cclaunch/PC1053/mosfet_board.kicad_sch

## KiCad design mosfet_board.kicad_sch (2026-06-03)

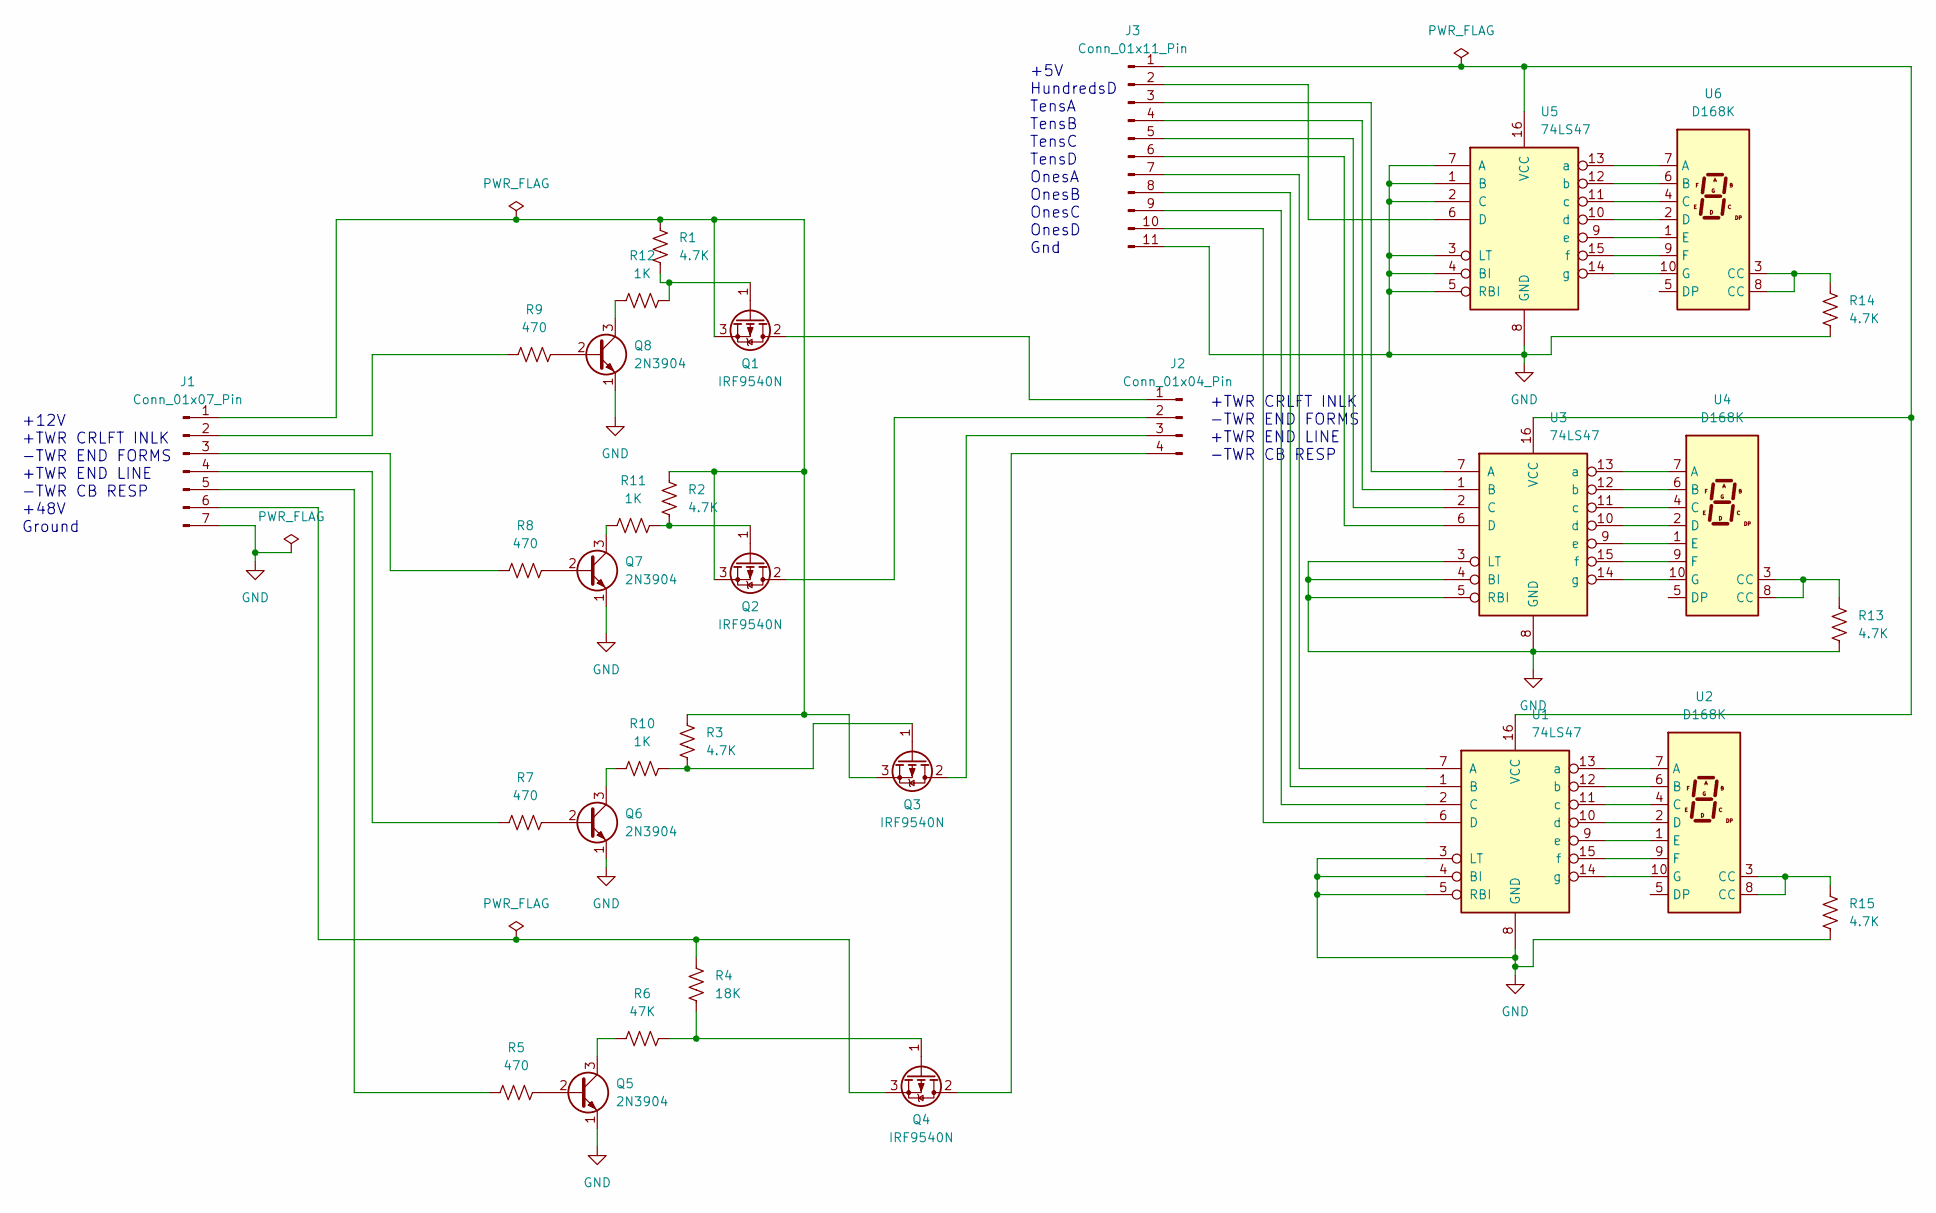
[picture p19: schematic mosfet_board.kicad_sch]

Parts:
J1: Conn_01x07_Pin
J2: Conn_01x04_Pin
J3: Conn_01x11_Pin
Q1, Q2, Q3, Q4: IRF9540N; TO-220-3_Vertical
Q5, Q6, Q7, Q8: 2N3904; TO-92_Inline
R1, R2, R3, R13, R14, R15: 4.7K
R4: 18K
R5, R7, R8, R9: 470
R6: 47K
R10, R11, R12: 1K
U1, U3, U5: 74LS47
U2, U4, U6: D168K; D1X8K

Connections:
GND: J1.7, J3.11, Q5.1 (E), Q6.1 (E), Q7.1 (E), Q8.1 (E), R13.2, R14.2, R15.2, U1.3 (LT), U1.4 (BI), U1.5 (RBI), U1.8 (GND), U3.3 (LT), U3.4 (BI), U3.5 (RBI), U3.8 (GND), U5.1 (B), U5.2 (C), U5.3 (LT), U5.4 (BI), U5.5 (RBI), U5.7 (A), U5.8 (GND)
unnamed: J1.1, Q1.3 (S), Q2.3 (S), Q3.3 (S), R1.1, R2.1, R3.1
unnamed: J1.2, R9.1
unnamed: J1.3, R8.1
unnamed: J1.4, R7.1
unnamed: J1.5, R5.1
unnamed: J1.6, Q4.3 (S), R4.1
unnamed: J2.1, Q1.2 (D)
unnamed: J2.2, Q2.2 (D)
unnamed: J2.3, Q3.2 (D)
unnamed: J2.4, Q4.2 (D)
unnamed: J3.1, U1.16 (VCC), U3.16 (VCC), U5.16 (VCC)
unnamed: J3.2, U5.6 (D)
unnamed: J3.3, U3.7 (A)
unnamed: J3.4, U3.1 (B)
unnamed: J3.5, U3.2 (C)
unnamed: J3.6, U3.6 (D)
unnamed: J3.7, U1.7 (A)
unnamed: J3.8, U1.1 (B)
unnamed: J3.9, U1.2 (C)
unnamed: J3.10, U1.6 (D)
unnamed: Q1.1 (G), R1.2, R12.2
unnamed: Q2.1 (G), R2.2, R11.2
unnamed: Q3.1 (G), R3.2, R10.2
unnamed: Q4.1 (G), R4.2, R6.2
unnamed: Q5.2 (B), R5.2
unnamed: Q5.3 (C), R6.1
unnamed: Q6.2 (B), R7.2
unnamed: Q6.3 (C), R10.1
unnamed: Q7.2 (B), R8.2
unnamed: Q7.3 (C), R11.1
unnamed: Q8.2 (B), R9.2
unnamed: Q8.3 (C), R12.1
unnamed: R13.1, U4.3 (CC), U4.8 (CC)
unnamed: R14.1, U6.3 (CC), U6.8 (CC)
unnamed: R15.1, U2.3 (CC), U2.8 (CC)
unnamed: U1.9 (e), U2.1 (E)
unnamed: U1.10 (d), U2.2 (D)
unnamed: U1.11 (c), U2.4 (C)
unnamed: U1.12 (b), U2.6 (B)
unnamed: U1.13 (a), U2.7 (A)
unnamed: U1.14 (g), U2.10 (G)
unnamed: U1.15 (f), U2.9 (F)
unnamed: U3.9 (e), U4.1 (E)
unnamed: U3.10 (d), U4.2 (D)
unnamed: U3.11 (c), U4.4 (C)
unnamed: U3.12 (b), U4.6 (B)
unnamed: U3.13 (a), U4.7 (A)
unnamed: U3.14 (g), U4.10 (G)
unnamed: U3.15 (f), U4.9 (F)
unnamed: U5.9 (e), U6.1 (E)
unnamed: U5.10 (d), U6.2 (D)
unnamed: U5.11 (c), U6.4 (C)
unnamed: U5.12 (b), U6.6 (B)
unnamed: U5.13 (a), U6.7 (A)
unnamed: U5.14 (g), U6.10 (G)
unnamed: U5.15 (f), U6.9 (F)

Notes on the sheet:
+12V +TWR CRLFT INLK -TWR END FORMS +TWR END LINE -TWR CB RESP +48V Ground
+TWR CRLFT INLK -TWR END FORMS +TWR END LINE -TWR CB RESP
+5V HundredsD TensA TensB TensC TensD OnesA OnesB OnesC OnesD Gnd
